mlab-modules/BATDATUNIT01/doc/gen/dxf/BATDATUNIT01-User_Comments.dxf

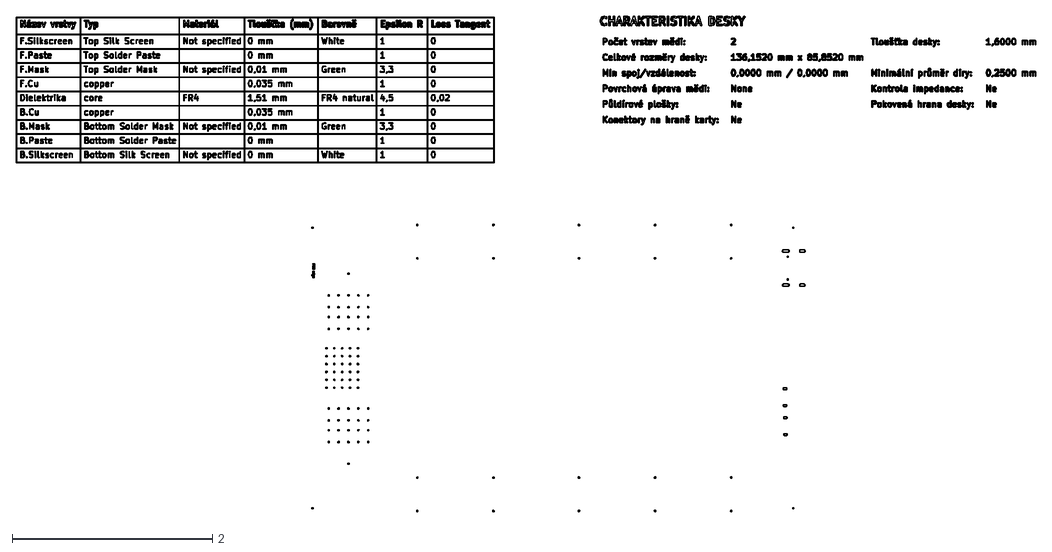
[picture p18: CAD file, 2026-02-07]
doc/gen/dxf/BATDATUNIT01-User_Comments.dxf
10.2 x 4.95
