mlab-modules/BATDATUNIT01/doc/gen/dxf/BATDATUNIT01-Edge_Cuts.dxf

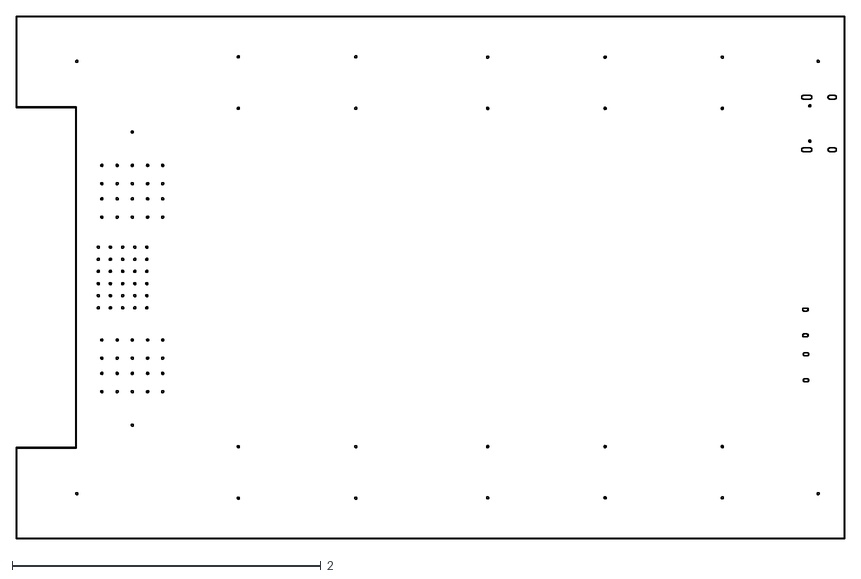
[picture p19: CAD file, 2026-02-07]
doc/gen/dxf/BATDATUNIT01-Edge_Cuts.dxf
5.36 x 3.38
